mariuszelectro/Nissan-ARIYA-motor-temperature-monitoring-/ExtraInfo/IMG_2094.jpeg

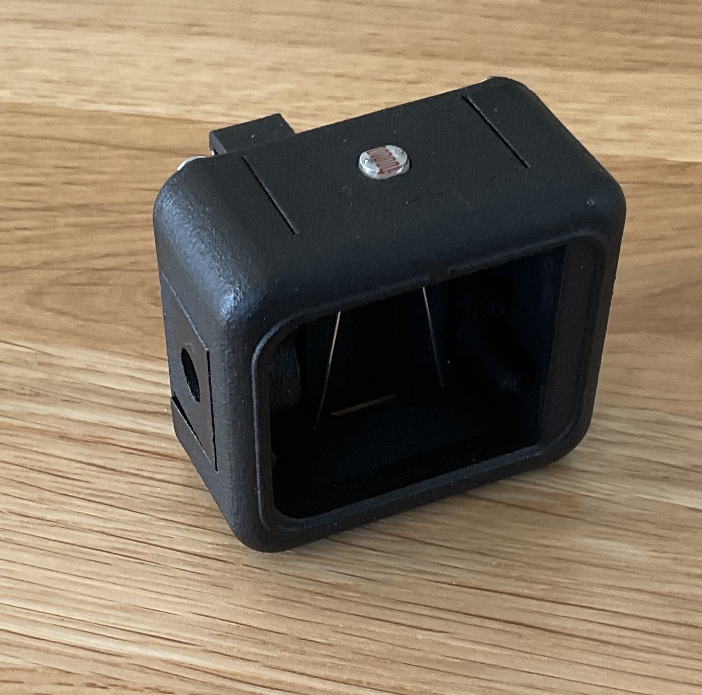
ExtraInfo/IMG_2094.jpeg
