mariuszelectro/Nissan-ARIYA-motor-temperature-monitoring-/ExtraInfo/IMG_2095.jpeg

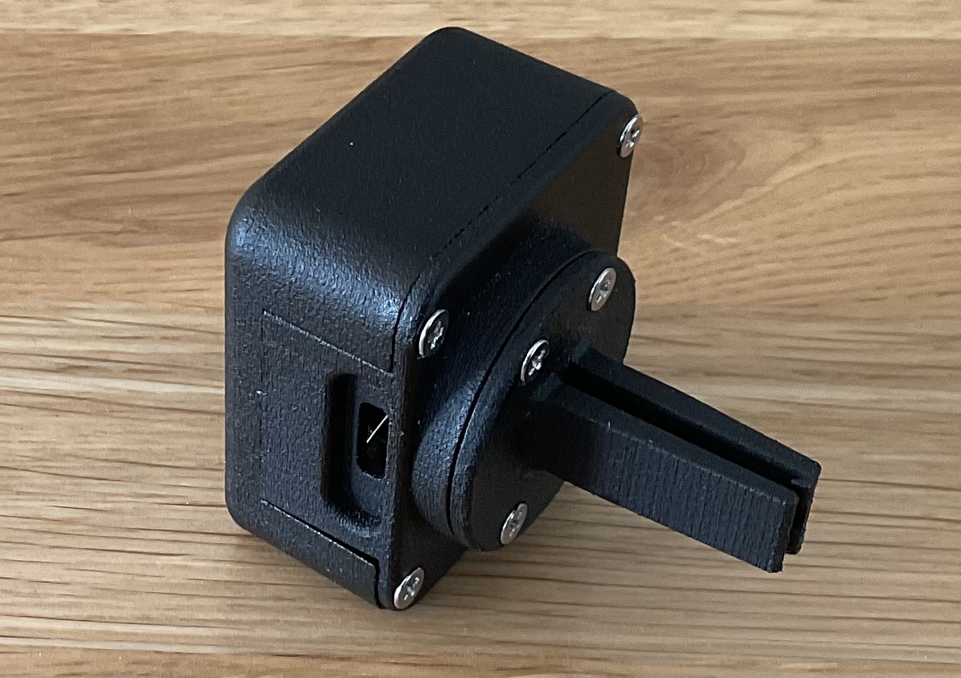
ExtraInfo/IMG_2095.jpeg
