mariuszelectro/Nissan-ARIYA-motor-temperature-monitoring-/ExtraInfo/IMG_2096.jpeg

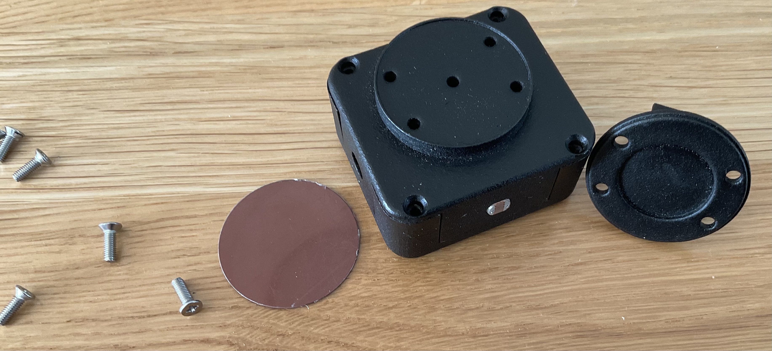
ExtraInfo/IMG_2096.jpeg
