mariuszelectro/Nissan-ARIYA-motor-temperature-monitoring-/ExtraInfo/IMG_2097.jpeg

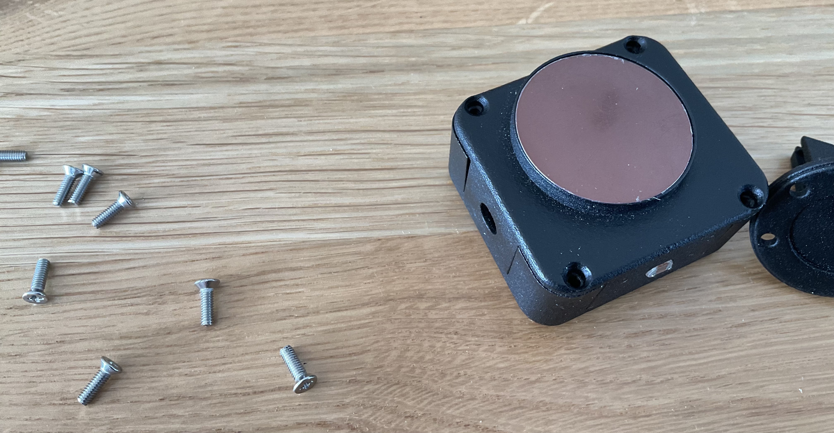
ExtraInfo/IMG_2097.jpeg
