mariuszelectro/Nissan-ARIYA-motor-temperature-monitoring-/ExtraInfo/IMG_2098.jpeg

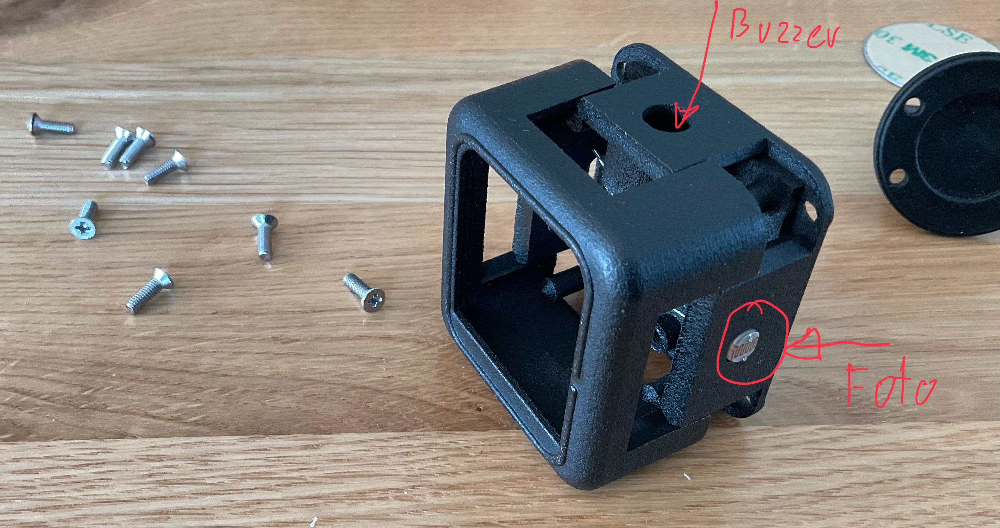
ExtraInfo/IMG_2098.jpeg
