mariuszelectro/Nissan-ARIYA-motor-temperature-monitoring-/ExtraInfo/IMG_2099.jpeg

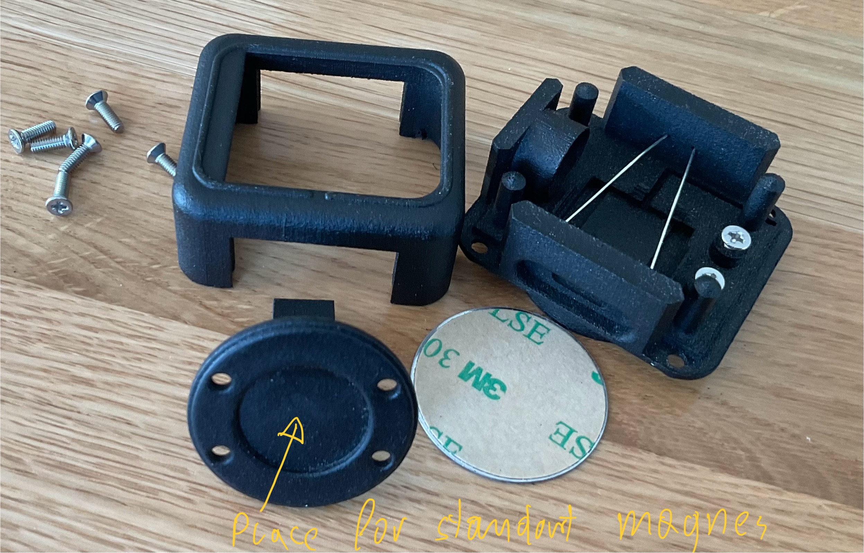
ExtraInfo/IMG_2099.jpeg
