mariuszelectro/Nissan-ARIYA-motor-temperature-monitoring-/ExtraInfo/IMG_2100.jpeg

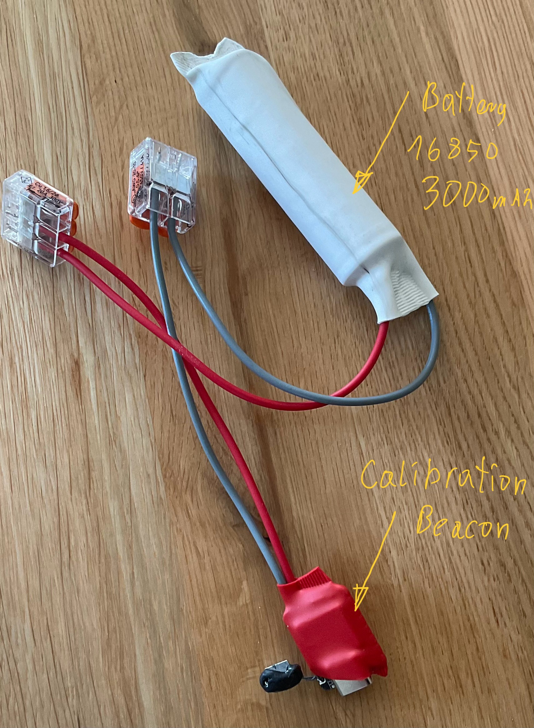
ExtraInfo/IMG_2100.jpeg
