mariuszelectro/Nissan-ARIYA-motor-temperature-monitoring-/ExtraInfo/IMG_2101.jpeg

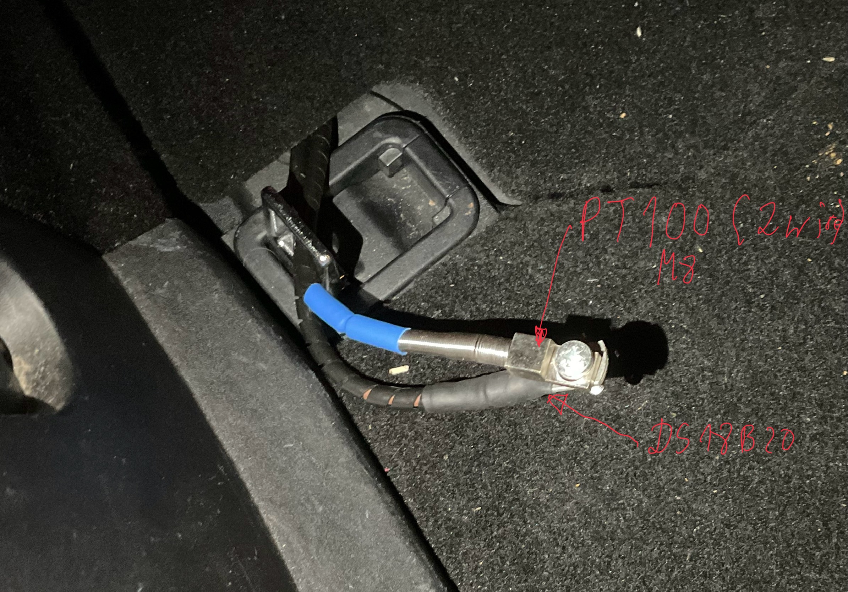
ExtraInfo/IMG_2101.jpeg
