mariuszelectro/Nissan-ARIYA-motor-temperature-monitoring-/ExtraInfo/IMG_2102.jpeg

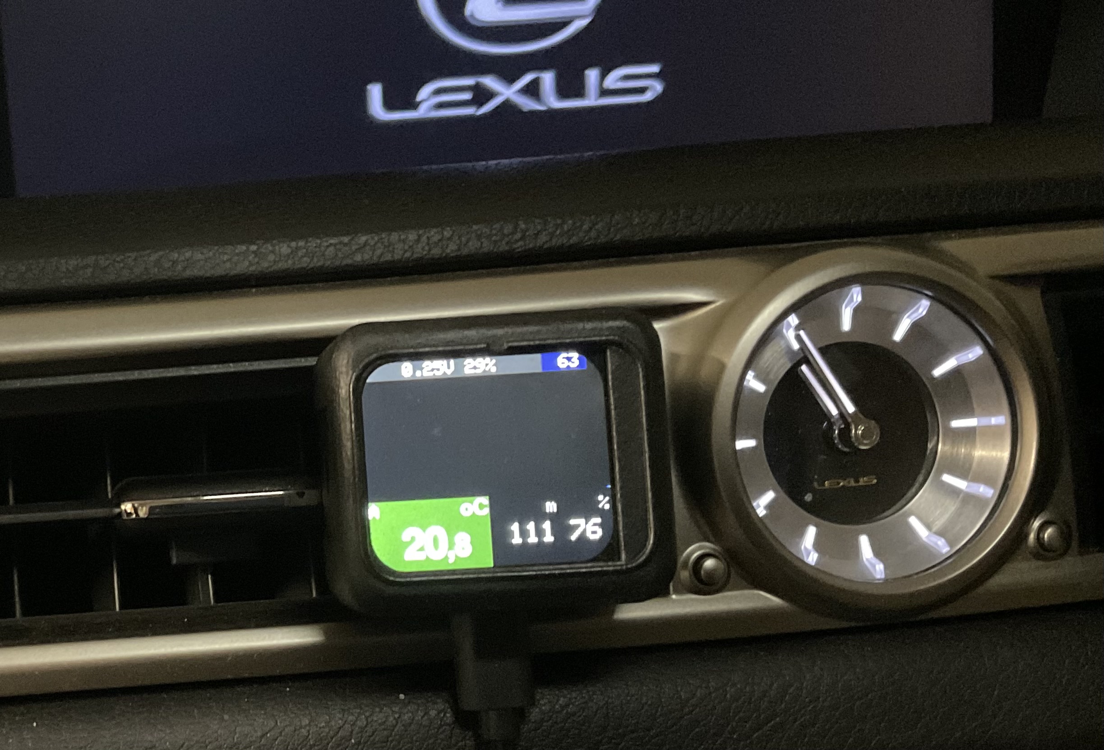
ExtraInfo/IMG_2102.jpeg
