mariuszelectro/Nissan-ARIYA-motor-temperature-monitoring-/ExtraInfo/IMG_2105.jpeg

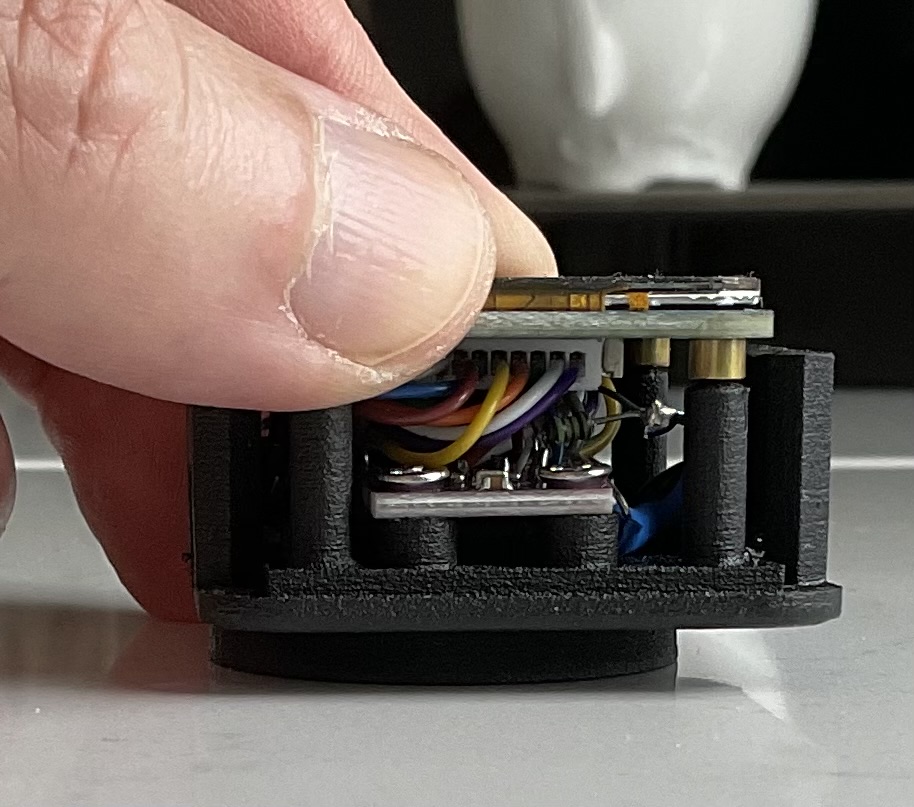
ExtraInfo/IMG_2105.jpeg
