mariuszelectro/Nissan-ARIYA-motor-temperature-monitoring-/ExtraInfo/IMG_2106.jpeg

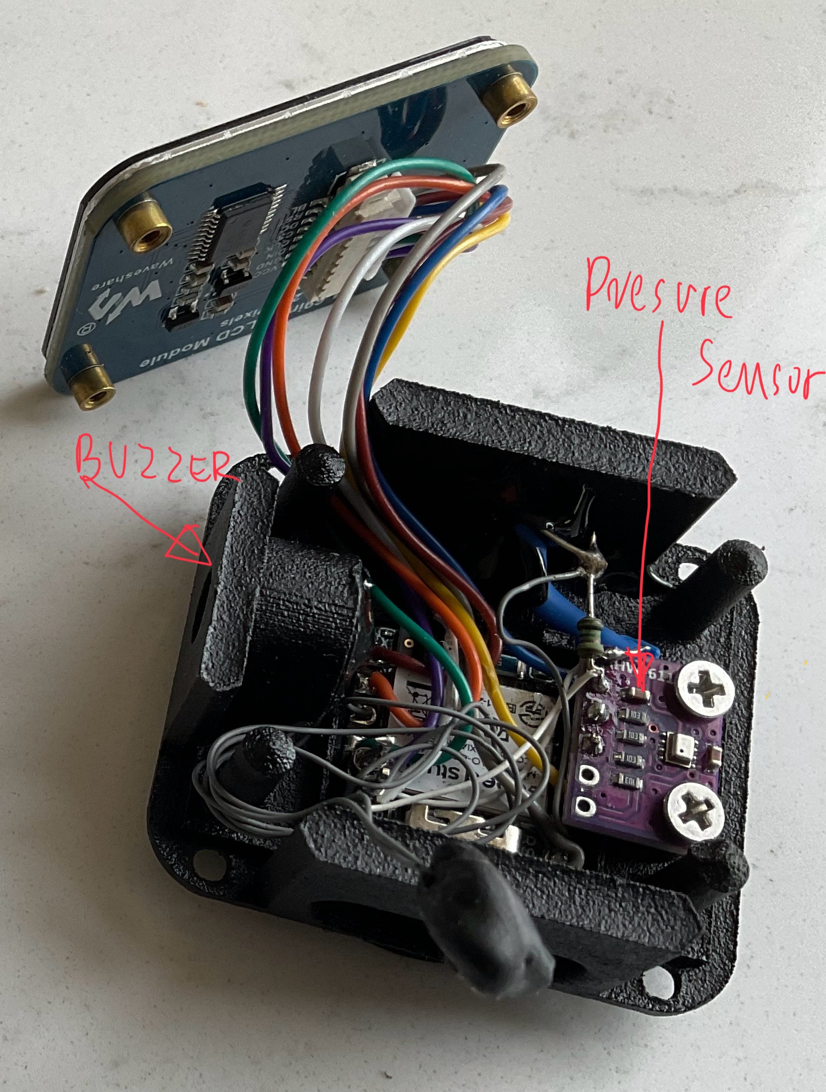
ExtraInfo/IMG_2106.jpeg
