mariuszelectro/Nissan-ARIYA-motor-temperature-monitoring-/ExtraInfo/IMG_2109.jpeg

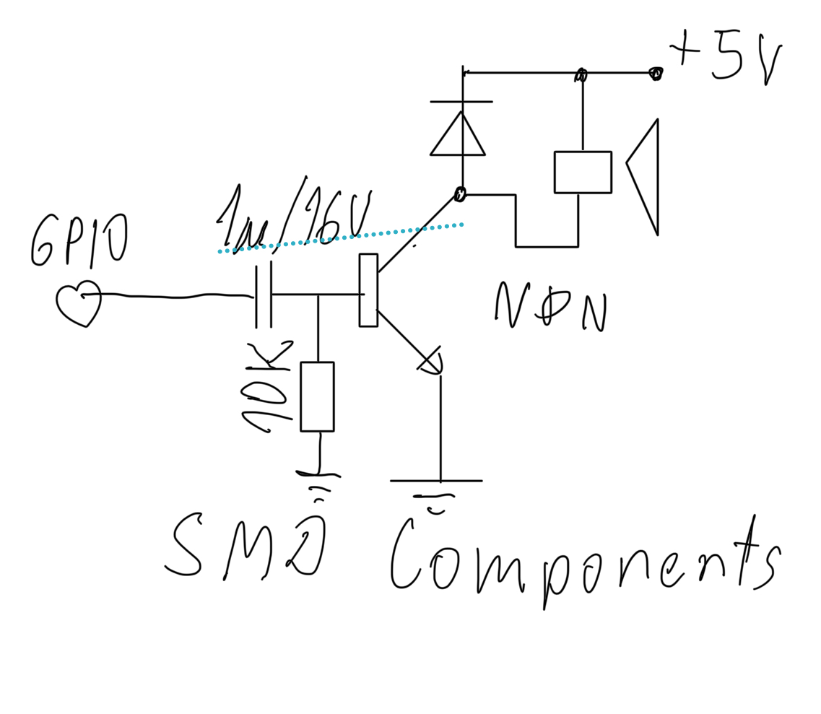
ExtraInfo/IMG_2109.jpeg
