mariuszelectro/Nissan-ARIYA-motor-temperature-monitoring-/ExtraInfo/IMG_4455.jpeg

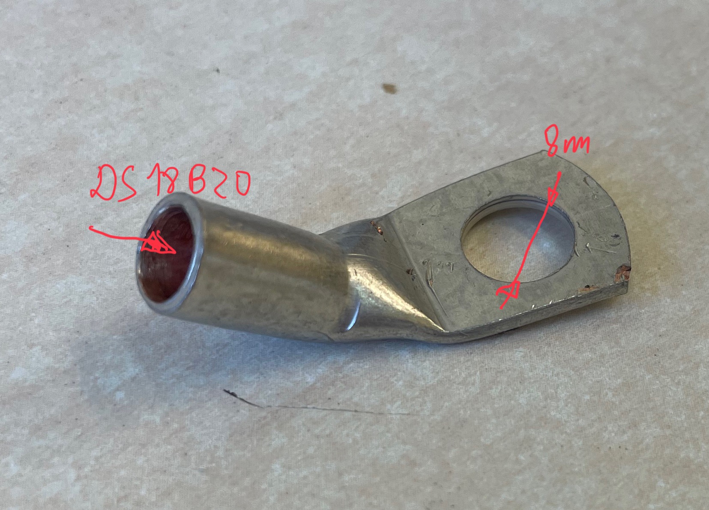
ExtraInfo/IMG_4455.jpeg
