mariuszelectro/Nissan-ARIYA-motor-temperature-monitoring-/ExtraInfo/IMG_4459.jpeg

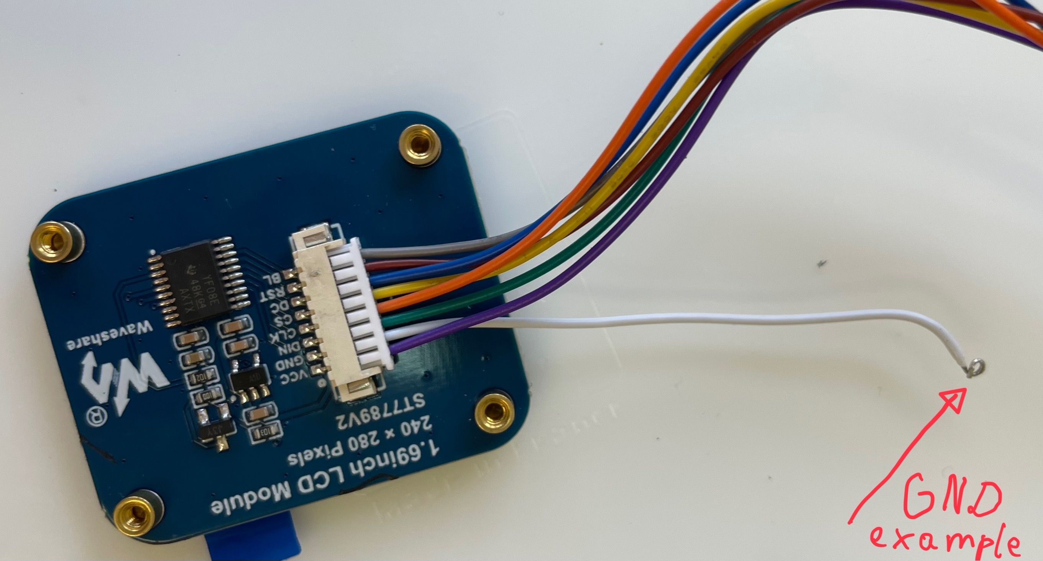
ExtraInfo/IMG_4459.jpeg
