mariuszelectro/Nissan-ARIYA-motor-temperature-monitoring-/ExtraInfo/IMG_4460.jpeg

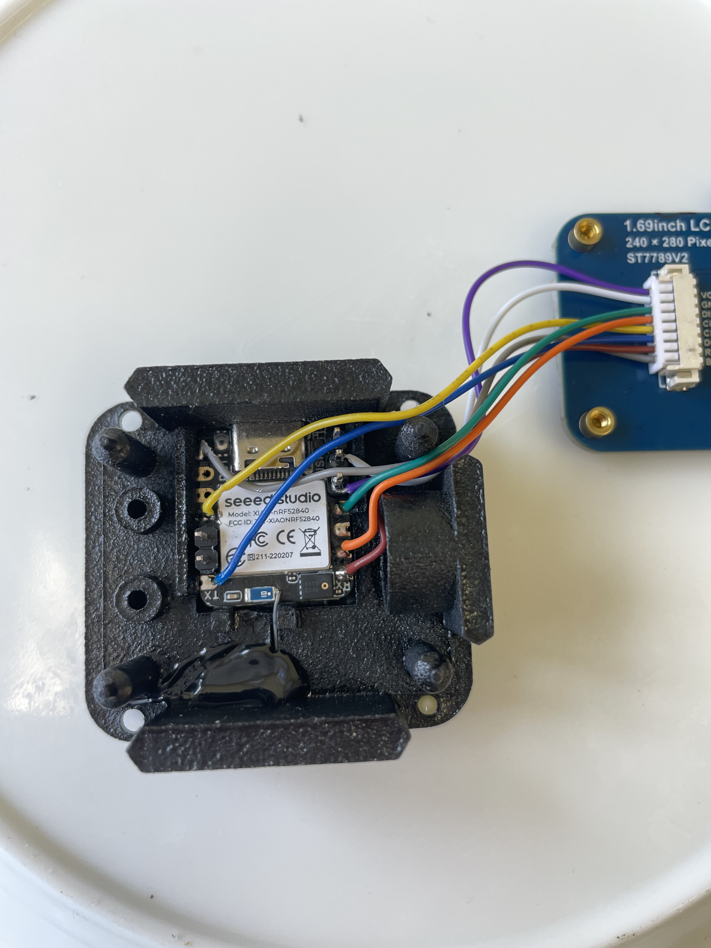
ExtraInfo/IMG_4460.jpeg
