mariuszelectro/Nissan-ARIYA-motor-temperature-monitoring-/ExtraInfo/IMG_4461.jpeg

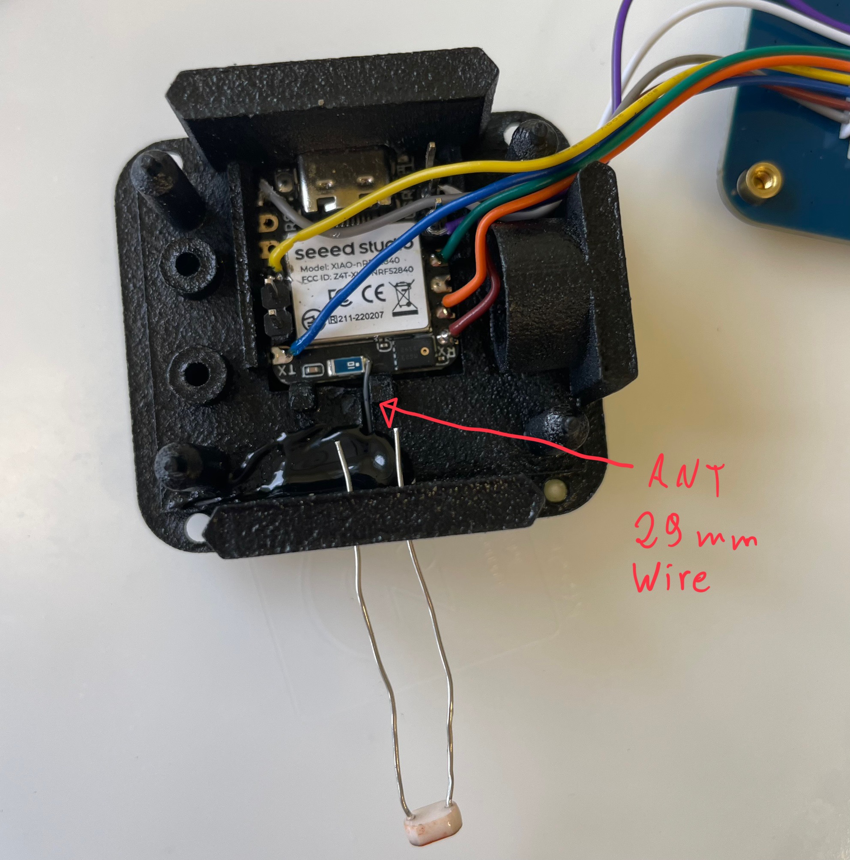
ExtraInfo/IMG_4461.jpeg
