mariuszelectro/Nissan-ARIYA-motor-temperature-monitoring-/ExtraInfo/IMG_4462.jpeg

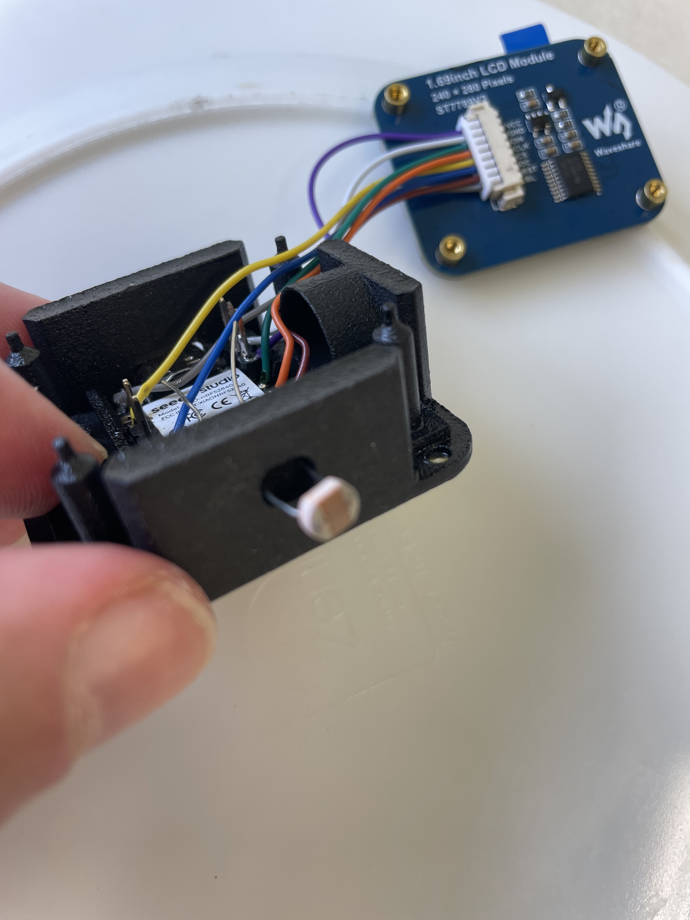
ExtraInfo/IMG_4462.jpeg
