mariuszelectro/Nissan-ARIYA-motor-temperature-monitoring-/ExtraInfo/IMG_4463.jpeg

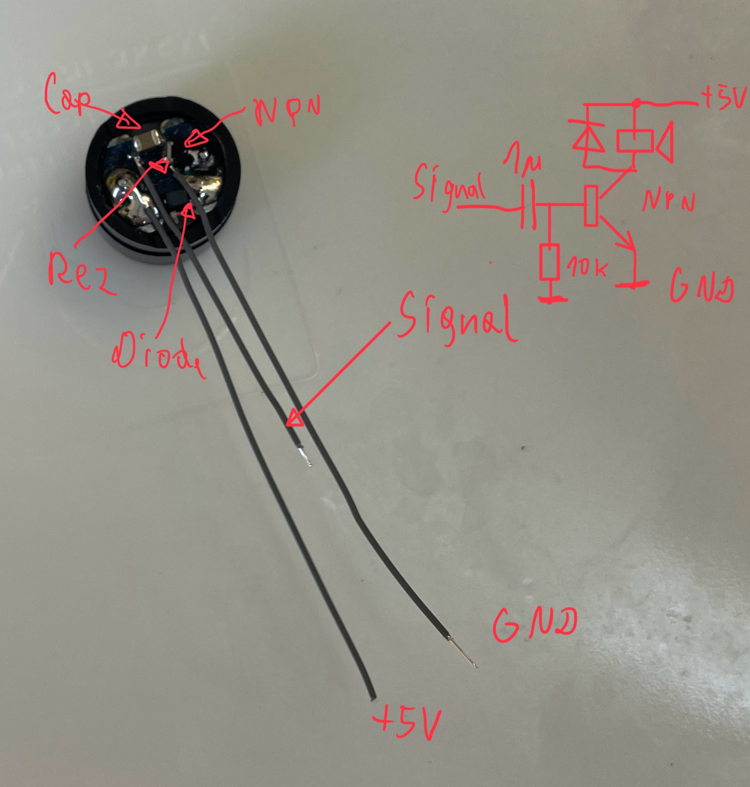
ExtraInfo/IMG_4463.jpeg
