mariuszelectro/Nissan-ARIYA-motor-temperature-monitoring-/ExtraInfo/IMG_4472.jpeg

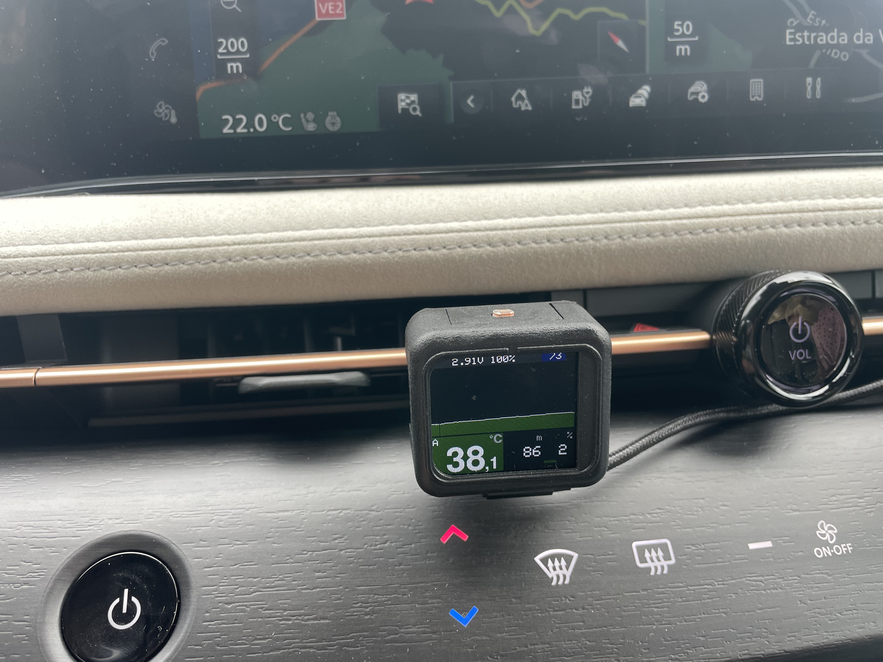
ExtraInfo/IMG_4472.jpeg
