mariuszelectro/Nissan-ARIYA-motor-temperature-monitoring-/ExtraInfo/oiY2WBU0hL0dvHHT.png

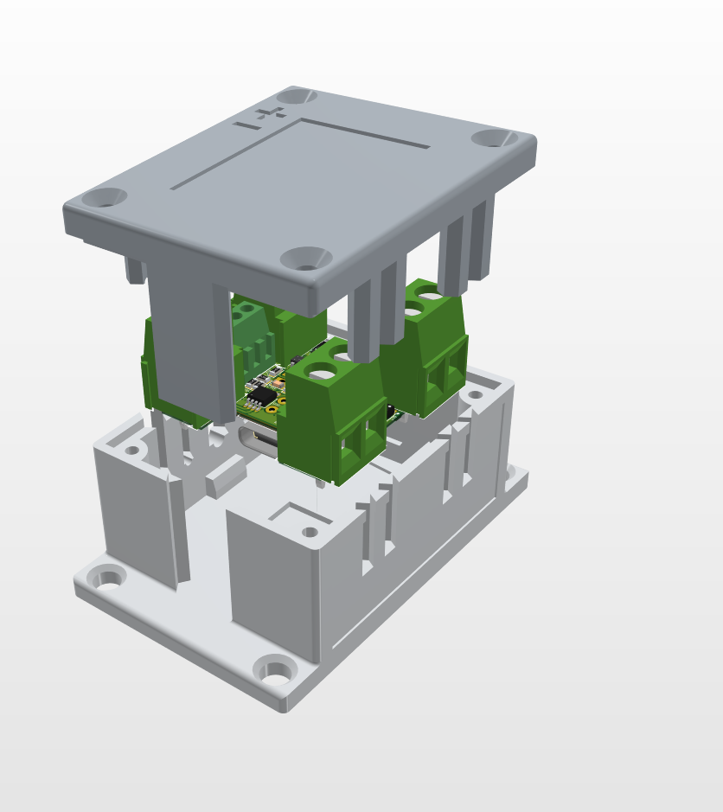
ExtraInfo/oiY2WBU0hL0dvHHT.png
