mariuszelectro/Nissan-ARIYA-motor-temperature-monitoring-/ExtraInfo/Puct6VyzmELIJFpL.png

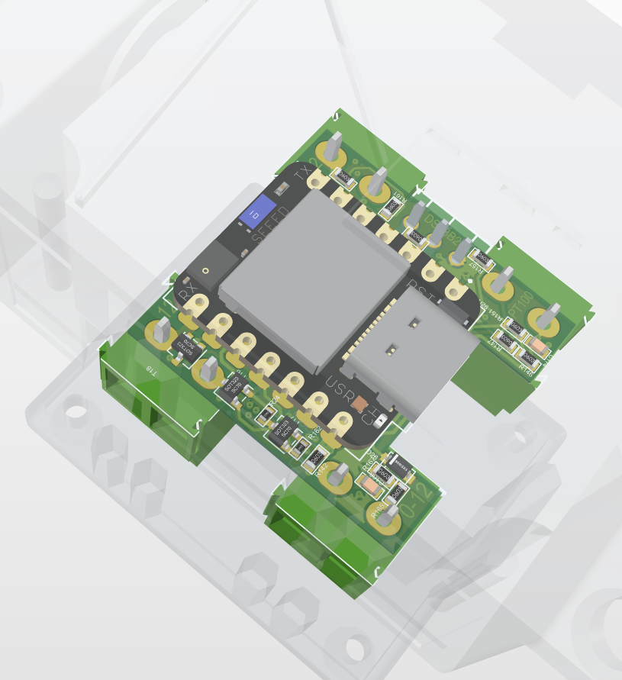
ExtraInfo/Puct6VyzmELIJFpL.png
