mariuszelectro/Nissan-ARIYA-motor-temperature-monitoring-/Receiver/FreeSansBold12pt7bMS.h

/*Modyfied https://tchapi.github.io/Adafruit-GFX-Font-Customiser orygional font for add missing ∘C character as 0x19 nad turtle symbol as 0x1A */
#pragma once
#include <Adafruit_GFX.h>

const uint8_t FreeSansBold12pt7bBitmapsMS[] PROGMEM = {
  0x31, 0xEC, 0xF3, 0xCD, 0xE3, 0x00, 0x03, 0xC0, 0x00, 0x7E, 0x00, 0x0F, 
  0xF0, 0x81, 0xFF, 0x9C, 0x3F, 0xFD, 0x47, 0xFF, 0xFC, 0x08, 0x10, 0x41, 
  0xC3, 0x80, 0xFF, 0xFF, 0xFF, 0xFF, 0x76, 0x66, 0x60, 0xFF, 0xF0, 0xFF, 
  0xFF, 0xFF, 0xFF, 0x76, 0x66, 0x60, 0xFF, 0xF0, 0xF3, 0xFC, 0xFF, 0x3F, 
  0xCF, 0x61, 0x98, 0x60, 0x0E, 0x70, 0x73, 0x83, 0x18, 0xFF, 0xF7, 0xFF, 
  0xBF, 0xFC, 0x73, 0x83, 0x18, 0x18, 0xC7, 0xFF, 0xBF, 0xFD, 0xFF, 0xE3, 
  0x18, 0x39, 0xC1, 0xCE, 0x0E, 0x70, 0x02, 0x00, 0x7E, 0x0F, 0xF8, 0x7F, 
  0xE7, 0xAF, 0xB9, 0x3D, 0xC8, 0x0F, 0x40, 0x3F, 0x00, 0xFF, 0x00, 0xFC, 
  0x05, 0xFF, 0x27, 0xF9, 0x3F, 0xEB, 0xEF, 0xFE, 0x3F, 0xE0, 0x7C, 0x00, 
  0x80, 0x04, 0x00, 0x3C, 0x06, 0x0F, 0xC1, 0x81, 0xFC, 0x30, 0x73, 0x8C, 
  0x0C, 0x31, 0x81, 0xCE, 0x60, 0x1F, 0xCC, 0x03, 0xF3, 0x00, 0x3C, 0x67, 
  0x80, 0x19, 0xF8, 0x02, 0x7F, 0x80, 0xCE, 0x70, 0x11, 0x86, 0x06, 0x39, 
  0xC1, 0x87, 0xF8, 0x30, 0x7E, 0x0C, 0x07, 0x80, 0x07, 0x80, 0x1F, 0xC0, 
  0x3F, 0xE0, 0x3C, 0xE0, 0x3C, 0xE0, 0x3E, 0xE0, 0x0F, 0xC0, 0x07, 0x00, 
  0x3F, 0x8C, 0x7F, 0xCC, 0xF1, 0xFC, 0xF0, 0xF8, 0xF0, 0x78, 0xF8, 0xF8, 
  0x7F, 0xFC, 0x3F, 0xDE, 0x1F, 0x8E, 0xFF, 0xFF, 0x66, 0x0C, 0x73, 0x8E, 
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
  {   728,  16,  18,  17,    1,  -17 },   // 0x43 'C'
  {   764,  15,  18,  17,    2,  -17 },   // 0x44 'D'
  {   798,  13,  18,  16,    2,  -17 },   // 0x45 'E'
  {   828,  12,  18,  15,    2,  -17 },   // 0x46 'F'
  {   855,  16,  18,  18,    1,  -17 },   // 0x47 'G'
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
};

const GFXfont FreeSansBold12pt7bMS PROGMEM = {
    (uint8_t *)FreeSansBold12pt7bBitmapsMS,  (GFXglyph *)FreeSansBold12pt7bGlyphsMS, 0x19, 0x7E,  29};

// Approx. 2858 bytes
